Tomasz-Zdeb/Embedded-Systems-Class-Project/schematics/Embedded-Systems-Class-Project/Embedded-Systems-Class-Project.kicad_pcb

## KiCad design schematics/Rotor_kicad/Rotor_kicad.kicad_sch

Schematic: Rotor_kicad.kicad_sch

Parts:
AR2: R_Array_SIP9
C1: 1 uF
C2, C3, C4, C5, C6, C7, C8, C10, C11, C18, C19, C21, C22: 100n
C9: 150n
C12, C16, C17: 1u
C13: (no value)
C14: 470p
C15: 220u 100V
C20: 100u 100V
CN1: Mechanical section connector
CN1L: LIOD interface connector
CN1_L: .
CN2: Line interface connector
CN2B, CN2_L: Front panel
CN2L: "Debit reader"
CN3L1: LIOD cable
CN3_L: Headset
CN4: Battery
CN5_L: Coin tray
CN6: Ext safe
CN6_L: LIOD
CNA: (no value)
CNB: (no value)
CNC: (no value)
CN_COIN: Coin discriminator module
CN_LCD, CN_LCD1: LCD module cable connector
CN_LCD2: Hitachi LM039 LCD module
D1: 1FK
D2, D4: 1N4148; D_DO-35_SOD27_P7.62mm_Horizontal
D3, D16, D17, D18: ?; D_DO-41_SOD81_P10.16mm_Horizontal
D5, D6, D7, D8, D9, D10, D11, D12, D13, D14, D15: 1N4007; D_DO-41_SOD81_P10.16mm_Horizontal
D22, D24, D25: BAS16W; SOT-323_SC-70
D23: "225"; SOT-323_SC-70
DL1: F.S. LED
DL2: LED
DZ1, DZ4: .
DZ2: 2.7V
DZ3: 18V
DZ5: 8.2V
DZ6: 1N5988
F5: Fuse
H1, H2, H4, H5, H6, H7, H8: (no value)
H3: 67382
H9: 67476 hybrid
J1, J2: .
J3: (no value)
J4: Conn_02x30_Odd_Even
JP1: (no value)
L1: L_Iron
ML1: 64357/A
MR1: .
OP1, OP2, OP3, OP4: CNY17-1
PM1: 4.7K
PM2: 100K
PTC1, PTC2, PTC3, PTC4: .
Q1, Q2, Q5, Q7, Q9, Q10: BC847; SOT-23
Q3, Q4, Q6, Q8: BC857; SOT-23
Q11: Si2301; SOT-23
R1, R5: (no value)
R2, R26, R40: 10K
R3: 150
R4: 100k?
R6: 47k
R7, R25, R63, R64: 100k
R8: 120K
R9: 3.9k
R10, R11, R15, R20, R21, R22, R23: ?
R12: 8.3K 1%
R13, R14: 122 1%
R16, R29, R30, R32, R33, R39, R48, R69: 100
R17: 620K 1%
R18: 100k(?)
R19: 13K
R24, R38: 150K
R27, R28, R34, R44, R60: 100K
R31, R41: 2.2K
R35: 1K
R36: 6.8K
R37: 300K
R42: 3.3K
R43: 46K
R45, R50, R51, R58, R59: 6.5K
R46, R47: 210
R49: 10
R52, R57: 330
R53, R54, R55, R56: 220
R61: 170k
R62: 11.6k
R65, R67, R68: 10k
R66: 20.8k
RL1, RL2: SIEMENS-V23042-B2201-B101
RN1: AR1; R_Array_SIP9
SUR1: (no value)
SW: RESET
SW1: Left
SW2: Right
SW3: 3
SW4: 4
SW5: 5
SW6: 6
SW7: 7
SW8: 8
SW9: *
SW10: 0
SW11: #
SW12: SW_SPST
SWH: Hookswitch
SWR: Redial button
T1, T10: BC327; TO-92_Inline
T2, T4, T6: BC337; TO-92_Inline
T3: MPSA92; TO-92_Inline
T5, T7, T8: MPSA42; TO-92_Inline
T9: BU806
T11, T12: BC237; TO-92_Inline
U1: 74HC14
U2, U9: 74LS125
U3, U4: 74HC244
U5: HEF4093B
U6: 74HC373
U7: 74LS148
U8: 4556
U10: 4023
U11: 4001
U12: ITR9608-F; Everlight_ITR9608-F

Connections:
+5V: AR2.1 (common), C6.2, C7.2, C8.2, C9.2, C10.2, C11.2, C12.2, C13.1, CN1.2, CN1.9, CN1.43, CN1.47, CN2.12, CN2.29, CN3L1.8, CNA.3, CNA.16, CNA.17, CNA.30, CNC.23, H2.4 (VCC), H3.9 (VCC), H4.4 (VCC), H5.4 (VCC), H6.8 (VCC), H7.8 (VCC), H8.8 (VCC), H9.7, J2.4, J3.7, R1.1, R2.1, R3.1, R4.1, R5.1, R7.1, R8.1, R10.1, R11.1, R12.1, R13.1, R14.1, R25.1, R63.1, R64.1, RL1.9 (15), RL1.10 (16), RN1.1 (common), U1.20 (VCC), U2.14 (VCC), U3.20 (VCC), U4.14 (VDD), U4.20 (VCC), U5.14 (D5), U5.20 (VCC), U6.14 (VCC), U6.20 (VCC), U7.16 (VCC), U8.8 (Vss), U8.16 (Vdd), U9.14 (VCC), U10.2, U10.8, U10.14 (VDD), U11.14 (VDD)
+BATT: C14.1, CN1.36, CN1.42, CN1.44, CN1.46, CN1L.7, CN2.13, CN2.28, CN3L1.5, H1.13 (OUT), H5.15 (VBAT1), H5.16 (VBAT2), J2.15, J2.16, Q3.2 (E), R16.1, R46.1, SUR1.1 (VBAT)
AC_DIN: CN1_L.31, CN2.31, T1.1 (C)
AC_DOUT: CN1_L.9, CN2.9, H1.1 (OUT), OP2.1
AS_BRIDGE_+: C14.2, D11.1 (K), D12.1 (K), R24.2, R25.1, T5.3 (E), T6.3 (C), T7.3 (C)
AS_DIN: CN1_L.33, CN2.33, JP1.1 (A), OP3.5
AS_DOUT: CN1_L.8, CN2.8, H1.3 (OUT), OP4.1
B_A0: CNB.21, U5.3 (D0), U6.3
B_A1: CNB.12, U5.4 (D1), U6.4
B_A2: CNB.22, U5.7 (D2), U6.7 (GND)
B_A3: CNB.11, U5.8 (D3), U6.8
B_A4: CNB.23, U5.13 (D4), U6.13
B_A5: CNB.10, U5.14 (D5), U6.14 (VCC)
B_A6: CNB.24, U5.17 (D6), U6.17 (D6)
B_A7: CNB.9, U5.18 (D7), U6.18 (D7)
CLOCK: CN_LCD.3, CN_LCD2.4
CN1-21: CN1.21, CN1.38
CN1-23: CN1.23, CN1.31
CN1-53: CN1.53, H9.8
CN1L-1: CN1L.1, U1.7 (GND), U1.18 (1Y0)
CN1L-3: CN1L.3, U1.9, U1.16 (1Y1)
CN1L-4: CN1L.4, D1.1 (K), D2.1 (K)
CN1L-5: CN1L.5, CN2L.2, CN3L1.2, R22.1, R23.1, T1.2 (B)
CN2-16: H9.6
CN2-18: CN2.18, CNC.14
CN2-21: U11.3, U11.12
CN2-22: CN2.22, H4.11 (OUT), R15.2
CN2-31: R17.1, U10.1
CN2-34: CN2.34, H1.5 (OUT)
CN2L-1: CN1L.10, CN2L.1, R3.2
CN2L-3: CN2L.3, R16.2
COIN_D0: CN1.51, U7.5 (EI)
COIN_D1: CN1.48, U7.11 (I1)
COIN_D2: CN1.11, U7.12 (I2)
COIN_D3: CN1.50, U7.13 (I3)
COIN_D4: CN1.12, U7.1 (I4)
COIN_D5: CN1.49, U7.2 (I5)
COIN_D6: CN1.13, U7.3 (I6)
COIN_SW1: CN2.10, H2.3 (IN)
COIN_SW2: CN2.32, H2.2 (IN)
C_A0: CNC.28, U5.2 (O0)
C_A1: CNC.7, U5.5 (O1)
C_A2: CNC.26, U5.6 (O2)
C_A3: CNC.8, U5.9 (O3)
C_A4: CNC.25, U5.12 (O4)
C_A5: CNC.24, U5.15 (O5)
C_A6: CNC.10, U5.16 (O6)
C_A7: CNC.22, U5.19 (O7)
C_A8: CNC.11, U6.2
C_A9: CNC.9, U6.12
C_A10: CNC.27
C_D0: CNB.1, CNC.29, RN1.3 (R2), U3.18 (1Y0), U4.18 (1Y0)
C_D1: CNB.32, CNC.31, RN1.5 (R4), U3.16 (VDD), U4.16 (1Y1)
C_D2: CNB.2, CNC.2, RN1.7 (R6), U3.14 (CLK), U4.14 (VDD)
C_D3: CNB.31, CNC.3, RN1.9 (R8), U3.12 (Cout), U4.12
C_D4: CNB.3, CNC.30, RN1.8 (R7), U2.3, U3.9 (Q8), U4.9
C_D5: CNB.30, CNC.4, H2.5 (OUT), RN1.6 (R5), U2.6, U3.7 (Q3), U4.7 (VSS)
C_D6: CNB.4, CNC.5, RN1.4 (R3), U2.8, U3.5 (Q6), U4.5
C_D7: CNB.29, CNC.6, RN1.2 (R1), U2.11, U3.3 (Q0), U4.3
C_S0: CNC.19, U6.5
C_S1: CNC.21, U6.6
C_S2: CNC.15
C/~D: CN_LCD.5, CN_LCD2.8
DATA: CN_LCD.11, CN_LCD2.5
ENC0: AR2.5 (R4), C1.2, CN1.35, U3.2 (Q1)
ENC1: AR2.4 (R3), C2.2, CN1.27, U3.4 (Q2)
ENC2: AR2.6 (R5), C3.2, CN1.34, U3.6 (Q7)
ENC3: AR2.8 (R7), C4.2, CN1.28, U3.8 (VSS)
ENC4: AR2.9 (R8), C5.2, CN1.33, U3.11 (Q9)
FS_LED: CN1.6, H1.13 (OUT)
GND: C1.1, C2.1, C3.1, C4.1, C5.1, C6.1, C7.1, C8.1, C9.1, C10.1, C11.1, C12.1, C13.2, C14.2, C16.1, C17.1, C22.1, CN1.16, CN1.20, CN1.22, CN1.26, CN1.29, CN1.52, CN1.59, CN1.60, CN2.11, CN2.30, CN2L.4, CN2L.7, CN3L1.4, CN3L1.7, CN6.3, CNA.1, CNA.32, CNC.1, CNC.16, CNC.17, CNC.32, D16.2 (A), D18.2 (A), D23.1 (A), D24.1 (A), H1.14 (GND), H2.12 (GND), H3.5 (GND), H4.12 (GND), H5.1 (GND1), H5.2 (GND2), H5.6 (GND3), H5.8 (GND4), H5.9 (GND5), H5.10 (GND6), H5.17 (GND7), H5.20 (GND8), H6.5 (GND1), H6.10 (GND2), H7.5 (GND1), H7.10 (GND2), H8.5 (GND1), H8.10 (GND2), H9.1, H9.14, J2.1, J2.2, J2.6, J2.8, J2.9, J2.10, J2.11, J2.17, J2.20, J3.1, J3.14, Q1.2 (E), Q2.2 (E), Q4.3 (C), Q7.2 (E), Q9.2 (E), Q11.3 (D), R4.2, R5.1, R7.1, R9.2, R12.2, R15.2, R17.2, R18.2, R23.2, R45.2, R51.2, R53.1, R56.1, R58.2, R62.1, R65.2, R67.2, R68.1, SUR1.2 (GND1), SUR1.4 (GND2), T1.3 (E), T2.3 (C), T3.3 (E), T4.3 (E), T5.3 (E), U1.10, U2.7 (GND), U3.10 (Q4), U4.7 (VSS), U4.10, U5.7 (D2), U5.10 (GND), U6.7 (GND), U6.10, U7.4 (I7), U7.8 (GND), U7.10 (IO), U8.8 (Vss), U8.16 (Vdd), U9.7 (GND), U10.7 (VSS), U11.7 (VSS)
H4-3: H4.3 (IN), H4.5 (OUT), U3.17 (2A0)
H4-8: H4.8 (OUT2), H7.1 (IN1)
H8-4: H8.4 (IN2), U6.16 (O6)
H9-2: H9.2, U11.11
H9-11: H9.11, U4.8
H9-15: CN2.36, H9.15
HOOK: AR2.2 (R1), CN2.17, U2.2
KBD_1: CN1_L.2, CN2.2, CN2_L.15, D1.2 (A), SW4.2, SW5.2, SW6.2
KBD_2: CN1_L.1, CN2.1, CN2_L.3, D4.2 (A), SW7.2, SW8.2, SW9.2
KBD_3: CN1_L.40, CN2.40, CN2_L.14, CNB.15, R10.2, SW3.1, SW6.1, SW9.1, SW11.1
KBD_4: CN1_L.39, CN2.39, CN2_L.4, D3.2 (A), SW9.2, SW10.2, SW11.2
KBD_5: CN1_L.3, CN2.3, CN2_L.13, CNB.16, R12.2, SW1.1, SW4.1, SW7.1, SW9.1
KBD_6: CN1_L.38, CN2.38, CN2_L.5, D2.2 (A), SW1.2, SW2.2, SW3.2
KBD_7: CN1_L.4, CN2.4, CN2_L.12, CNB.18, R11.2, SW2.1, SW5.1, SW8.1, SW10.1
LCD_CLK: CN1.3, CNA.10
LCD_C/~D: CN1.5, CNA.8
LCD_MOSI: CN1.57, CNA.24
LIOD_RESET: CN3L1.10, U1.12
MCU-PC0: U5.1 (OE), U6.1
unnamed: C1.1, R3.1, U2.6, U2.11
unnamed: C1.2, D7.1 (K), D8.2 (A), R6.1, RL1.6 (9), U2.3
unnamed: C2.2, C3.2, C4.1, CN3L1.9, D2.2 (A), DZ3.1 (K), OP2.4, R9.2, R11.2, R24.1, RL2.8 (13), T2.1 (E), U1.2
unnamed: C3.1, U1.11
unnamed: C4.2, R12.1, R15.1, U1.10
unnamed: C5.1, U5.11 (LE)
unnamed: C5.2, Q11.1 (G), R62.2, U5.8 (D3), U5.9 (O3)
unnamed: C6.1, C7.1
unnamed: C6.2, R13.1
unnamed: C7.2, CN3_L.1
unnamed: C8.1, CN3_L.3, R16.2
unnamed: C8.2, C9.1, R17.2, U1.1
unnamed: C10.1, U1.5, U1.8
unnamed: C2.1, C10.2, C11.1, C12.2, C13.1, CN3_L.4, D5.2 (A), D7.2 (A), DZ3.2 (A), R10.1, R12.2, R18.1, R19.2, RL2.7 (11), U1.3, U1.9
unnamed: C9.2, C12.1, R17.1, U1.16 (1Y1)
unnamed: C13.2, R12.1, R15.2
unnamed: C14.1, OP4.5, R24.1, T7.2 (B)
unnamed: C15.1, D4.1 (K)
unnamed: C15.2, D9.2 (A), D10.2 (A), DL2.1 (K), DZ6.2 (A), R29.2, R42.1
unnamed: C18.1, R35.1, R36.2, T10.2 (B)
unnamed: C18.2, R34.2, R36.1, T10.3 (E), U2.8
unnamed: C19.1, U6.11, U6.12
unnamed: C19.2, Q11.2 (S), R65.1, U6.9
unnamed: C20.1, D13.2 (A), DZ5.1 (K), F5.2
unnamed: C20.2, CN4.1, DZ5.2 (A)
unnamed: C21.1, D24.3 (K), R67.1, U6.1
unnamed: C21.2, U6.3, U6.6
unnamed: C22.2, D25.3 (K), R68.2, U6.5
unnamed: CN1.40, R16.2
unnamed: CN1L.6, SUR1.3 (UNK)
unnamed: CN1L.9, CN1L.11, CN1L.12
unnamed: CN1_L.5, CN2_L.11
unnamed: CN1_L.10, CN5_L.4
unnamed: CN1_L.12, CN1_L.15
unnamed: CN1_L.14, CN6_L.2
unnamed: CN1_L.17, T11.1 (C)
unnamed: CN1_L.18, CN6_L.4
unnamed: CN1_L.22, CN6.5
unnamed: CN1_L.24, R39.1
unnamed: CN1_L.25, CN6_L.3
unnamed: CN1_L.27, CN6_L.1
unnamed: CN1_L.32, CN5_L.2
unnamed: CN1_L.34, CN6_L.10
unnamed: CN1_L.36, CN2_L.9
unnamed: CN2B.1, SWH.1 (A)
unnamed: CN2B.2, SWH.3 (C)
unnamed: CN2B.7, SWR.2 (B)
unnamed: CN2B.8, SWH.6 (C)
unnamed: CN2B.10, SWH.5 (B)
unnamed: CN2B.11, SWR.3 (C)
unnamed: CN2B.16, SWH.2 (B)
unnamed: CN2L.5, SUR1.5 (UNK2)
unnamed: CN2L.8, R10.1
unnamed: CN2L.9, D1.2 (A), R21.2
unnamed: CN2L.10, R10.2, T3.1 (C)
unnamed: CN2_L.1, MR1.2
unnamed: CN2_L.2, MR1.1
unnamed: CN2_L.6, CN2_L.8
unnamed: CN2_L.7, R39.2
unnamed: CN2_L.10, R40.1
unnamed: CN2_L.16, MR1.3
unnamed: CN3L1.1, R17.1, U1.6
unnamed: CN3L1.3, R18.1, U1.4
unnamed: CN3_L.2, R14.1
unnamed: CN4.2, F5.1
unnamed: CN5_L.1, CN5_L.3
unnamed: CN6.1, R33.2
unnamed: CN6.2, CN6.4, R32.1
unnamed: CN6_L.5, R25.2
unnamed: CN6_L.9, CN6_L.11, CN6_L.12
unnamed: CN_LCD1.1, J4.1
unnamed: CN_LCD1.2, J4.3
unnamed: CN_LCD1.3, J4.5
unnamed: CN_LCD1.4, J4.7
unnamed: CN_LCD1.5, J4.9
unnamed: CN_LCD1.6, J4.11
unnamed: CN_LCD1.7, J4.13
unnamed: CN_LCD1.8, J4.14
unnamed: CN_LCD1.9, J4.12
unnamed: CN_LCD1.10, J4.10
unnamed: CN_LCD1.11, J4.8
unnamed: CN_LCD1.12, J4.6
unnamed: CN_LCD1.13, J4.4
unnamed: CN_LCD1.14, J4.2
unnamed: CN_LCD.1, SW.1
unnamed: CN_LCD.2, CN_LCD2.2
unnamed: CN_LCD.6, CN_LCD2.10, DL1.2 (A)
unnamed: CN_LCD.7, SW2.2
unnamed: CN_LCD.8, SW1.1
unnamed: CN_LCD.13, CN_LCD.14, CN_LCD2.1, PM1.1, PM1.2, SW1.2
unnamed: D1.1 (K), OP2.5, R8.1, U8.11 (~Q1)
unnamed: D2.1 (K), U8.12 (~Q0)
unnamed: D2.2 (A), DZ4.1 (K), DZ5.2 (A), PTC3.2
unnamed: D3.1 (K), U8.9 (~Q3)
unnamed: D4.1 (K), U8.10 (~Q2)
unnamed: D4.2 (A), OP4.4, R26.1, R27.1, R28.1, R31.2, T5.1 (C), T8.3 (C)
unnamed: D5.1 (K), D6.2 (A), DZ1.1 (K), PTC1.2
unnamed: D6.1 (K), D8.1 (K), DZ2.1 (K), R4.1
unnamed: D2.1 (K), D10.1 (K), D12.2 (A), DZ5.1 (K), R23.1
unnamed: D9.1 (K), D11.2 (A), DZ4.2 (A), OP3.2, PTC4.2
unnamed: D13.1 (K), D14.2 (A)
unnamed: D14.1 (K), D15.2 (A)
unnamed: D3.2 (A), D16.1 (K), J2.12, Q6.3 (C), Q7.3 (C)
unnamed: D3.1 (K), D17.1 (K), Q3.3 (C), Q4.2 (E), Q6.2 (E), Q8.2 (E), R48.1, R54.2, R55.2
unnamed: D17.2 (A), D18.1 (K), J2.18, Q8.3 (C), Q9.3 (C)
unnamed: D22.1 (A), R66.1
unnamed: D22.3 (K), U5.1 (OE), U5.2 (O0), U5.4 (D1)
unnamed: D23.3 (K), R61.2, R66.2, U5.5 (O1)
unnamed: D25.1 (A), R69.2
unnamed: DL1.1 (K), DL2.2 (A), R3.1
unnamed: DL1.2 (A), R28.2, T8.2 (B)
unnamed: DZ1.2 (A), PTC2.2, R3.2, RL1.8 (13)
unnamed: DZ2.2 (A), OP1.2, R7.1, R8.2, RL2.6 (9), T2.3 (C), T3.1 (C)
unnamed: DZ6.1 (K), R29.1
unnamed: H1.15 (IN), H9.3
unnamed: H2.6 (OUT), U4.17 (2A0)
unnamed: H2.7 (OUT1), U4.13
unnamed: H3.2 (OUT), U2.5
unnamed: H3.4 (OUT), U2.12
unnamed: H3.6 (OUT), U4.15 (2A1)
unnamed: H3.7 (OUT), U2.9
unnamed: H3.10 (IN), R7.2, R9.2
unnamed: H4.6 (OUT), H6.1 (IN1)
unnamed: H4.7 (OUT1), U3.13 (CKEN)
unnamed: H4.9 (IN), U4.1, U4.19 (2OE), U8.7 (~Q3)
unnamed: H4.10 (IN), U2.1, U2.4, U2.10, U2.13, U8.5 (~Q1)
unnamed: H5.7 (DRV_EN), U11.4
unnamed: H6.4 (IN2), U6.15 (O5)
unnamed: H7.4 (IN2), U6.9
unnamed: H9.4, JP1.2 (B), R5.2
unnamed: H9.5, U10.5
unnamed: H9.10, U10.4
unnamed: H9.12, U10.3
unnamed: J1.1, R60.2, U1.1, U1.12
unnamed: J1.2, U1.2
unnamed: J1.3, U1.3, U1.8, U1.9
unnamed: J1.4, U1.6
unnamed: J1.6, U1.10
unnamed: J1.7, U1.13
unnamed: J1.5, J1.10
unnamed: J2.3, Q2.1 (B), U4.12
unnamed: J2.5, U4.8
unnamed: J2.7, U4.1, U4.2
unnamed: J3.2, U5.6 (O2)
unnamed: J3.3, R61.1, U5.3 (D0)
unnamed: J3.4, R63.2, U5.12 (O4)
unnamed: J3.5, U5.10 (GND)
unnamed: J3.6, R64.2, U5.13 (D4)
unnamed: J3.8, U6.13
unnamed: J3.9, U6.10
unnamed: J3.10, U6.8
unnamed: J3.11, U6.4
unnamed: J3.12, U6.2
unnamed: J3.13, R69.1
unnamed: ML1.4 (I_LIMIT), R43.1
unnamed: ML1. (GND), ML1.2 (GND), R44.2, T12.3 (E)
unnamed: MR1.4, RL1.7 (11)
unnamed: MR1.6, PTC1.1
unnamed: MR1.7, PTC2.1
unnamed: MR1.8, PTC3.1
unnamed: MR1.9, PTC4.1
unnamed: OP1.1, R4.2
unnamed: OP1.5, R5.2
unnamed: OP3.1, R23.2
unnamed: PM1.1, PM1.2, R30.1
unnamed: PM1.3, R42.2, T9.1 (B)
unnamed: PM2.1, R38.1
unnamed: PM2.2, U2.5
unnamed: PM2.3, R37.2
unnamed: Q1.1 (B), R22.2, R45.1
unnamed: Q1.3 (C), R47.2
unnamed: Q2.3 (C), R49.2
unnamed: Q3.1 (B), R46.2, R47.1
unnamed: Q4.1 (B), R48.2, R49.1
unnamed: Q5.1 (B), R50.2, R51.1
unnamed: Q5.2 (E), Q7.1 (B), R53.2
unnamed: Q5.3 (C), R52.2
unnamed: Q6.1 (B), R54.1, R57.1
unnamed: Q8.1 (B), R52.1, R55.1
unnamed: Q10.1 (B), R58.1, R59.1
unnamed: Q9.1 (B), Q10.2 (E), R56.2
unnamed: Q10.3 (C), R57.2
unnamed: R1.1, R2.1
unnamed: R1.2, T2.1 (E), U2.1, U3.14 (CLK)
unnamed: R2.1, R20.2, T6.2 (B)
unnamed: R2.2, U3.5 (Q6)
unnamed: R3.1, R4.1, T2.2 (B)
unnamed: R3.2, SW2.1
unnamed: R5.1, R6.2, T1.2 (B)
unnamed: R5.2, U1.2, U1.14 (VCC)
unnamed: R6.1, T1.3 (E)
unnamed: R6.2, U2.2
unnamed: R7.2, T3.2 (B), U1.5, U1.11
unnamed: R8.2, R9.1, T3.2 (B)
unnamed: R9.1, T2.2 (B), T3.3 (E)
unnamed: R10.2, U1.14 (VCC)
unnamed: R11.1, R12.2, U1.6
unnamed: R11.2, T4.1 (C), U1.13
unnamed: R12.1, T4.2 (B)
unnamed: R13.2, U1.12
unnamed: R14.2, U1.13
unnamed: R15.1, R16.1, T5.2 (B)
unnamed: R18.2, U1.7 (GND)
unnamed: R19.1, U1.4
unnamed: R20.1, T6.3 (C)
unnamed: R21.1, T6.1 (E)
unnamed: R22.1, U4.11
unnamed: R22.2, U3.9 (Q8)
unnamed: R24.2, T1.1 (C)
unnamed: R26.2, T5.2 (B), T6.1 (E)
unnamed: R27.2, T6.2 (B), T7.1 (E)
unnamed: R30.2, T8.1 (E)
unnamed: R31.1, T9.2 (C)
unnamed: R34.1, U2.3
unnamed: R35.2, U2.7 (GND)
unnamed: R37.1, T10.1 (C)
unnamed: R40.2, R41.1, T11.2 (B)
unnamed: R41.2, T11.3 (E)
unnamed: R43.2, R44.1, T12.2 (B)
unnamed: R50.1, U4.4
unnamed: R59.2, U4.6, U4.10
unnamed: RL2.9 (15), RL2.10 (16)
unnamed: T5.1 (C), U1.15 (2A1)
unnamed: U1.1, U2.9, U2.10
unnamed: U1.8, U2.12, U3.15 (Reset)
unnamed: U1.5, U1.11
unnamed: U1.5, U1.12
unnamed: U1.19 (2OE), U2.8
unnamed: U2.4, U2.5
unnamed: U3.1 (Q5), U3.19 (2OE), U8.6 (~Q2)
unnamed: U4.2, U7.9 (S0)
unnamed: U4.4, U7.7 (S1)
unnamed: U4.6, U7.6 (S2)
unnamed: U4.3, U4.5, U4.9, U4.13
unnamed: U10.6, U10.12
unnamed: U11.5, U11.10
PA0: CNA.26, H1.2 (IN)
PA1: CNA.7, H1.8 (IN)
PA2: CNA.27, H1.11 (IN)
PA3: CNA.6, U10.9
PA4: CNA.28, H1.4 (IN)
PA5: CNA.5
PA6: CNA.29, U8.14 (A0)
PA7: CNA.4, U8.13 (A1)
PB0: CNA.22, U11.1, U11.2
PB1: CNA.11, H1.6 (IN)
PB2: CNA.23, H2.9 (IN)
PC0: CN2.23, CNA.18, U8.1 (~EN), U8.15 (~EN), U10.11, U10.13, U11.6, U11.13
PC1: CN1.10, CNA.15
PC2: CNA.19, CNC.18, R2.2
PC3: CNA.14, H8.1 (IN1)
PC4: CNA.20, H2.10 (IN)
PC5: CN2.25, CNA.13, R3.2
PC6: CN2.27, CNA.21, R4.2
PD4: CNB.19, H9.9
PD5: CNB.14
PHOTO_POCKET: CN1.39, H3.8 (IN)
PHOTO_R_EXIT: CN1.45, R8.2, R9.1
PHOTO_R_IN: CN1.32, H3.1 (IN)
PHOTO_R_IN_PWR: CN1.30, CN2.24, H4.13 (OUT)
PHOTO_R_POCKET_PWR: CN1.17, R15.1
PHOTO_SAFE: CN1.41, H3.3 (IN)
REDIAL: CN2.5, H2.1 (IN)
RL1-R: CN1_L.6, CN2.6, H2.13 (OUT), RL1.1
RL1-S: CN1_L.37, CN2.37, H2.11 (OUT), RL1.2
RL2-R: CN1_L.7, CN2.7, H1.7 (OUT), RL2.1
RL2-S: CN1_L.35, CN2.35, H1.10 (OUT), RL2.2
R_MOT_A: CN1.24, H5.18 (MOT2)
R_MOT_B: CN1.37, H5.12 (MOT1)
SAFE_SW1: AR2.3 (R2), C17.2, CN1_L.19, CN2.19, R33.1, U4.11
SAFE_SW2: AR2.7 (R6), C16.2, CN1_L.20, CN2.20, R32.2, U3.15 (Reset)
SCL-39: CN2.15, CNB.17
SCL-43: CNB.25, U11.8, U11.9
SCL-44: CNB.8, H5.5 (DIR)
SCL-45: CNB.26, H5.3 (~RUN/STOP)
SCL-46: CN2.14, CNB.7
SCL-47: CNB.27, U5.11 (LE)
SCL-50: CNB.6, U6.11
SCL-51: CNB.28, U8.2 (A0)
SCL-52: CNB.5, U8.3 (A1), U8.4 (~Q0)
SOLENOID_C_PATH: CN1.19, H6.9 (SOL)
SOLENOID_C_REJ: CN1.15, H7.9 (SOL)
SOLENOID_R_POCKET: CN1.25, H8.9 (SOL)
SW1: CN1.54, CNB.13, R14.2
SW2: CN1.7, CNB.20, R13.2
SW_C_PATH: CN1.18, H4.1 (IN)
SW_C_REJ: CN1.14, H4.2 (IN)
V0: CN_LCD.12, CN_LCD2.3
~BUSY: CN_LCD.10, CN_LCD2.7, R2.2
~CS: CN_LCD.4, CN_LCD2.6
~IRQ: CNA.31, U10.10
~I_LIMIT: CN1_L.26, CN2.26, CNA.12, R1.2, T12.1 (C)
~LCD_BUSY: CN1.56, CNA.25
~LCD_CS: CN1.4, CNA.9
~LCD_RESET: CN1.55, U6.19 (O7)
~LIOD_RESET_BUFF: R8.1, R25.2, U1.3
~LIOD_RESET: CN1L.2, U1.17 (2A0), U2.13
~RST: CN1.1, CNA.2, CN_LCD.9, CN_LCD2.9, R1.2

Notes on the sheet:
No designators present on module. Resistors are thick-film on ceramic, laser trimmed. Reported values are direct measures.
Might be a zener
No designators present on module. Resistor are thick-film on ceramic, laser trimmed. Reported values are direct measures.
Pin numbering on silkscreen doesn't match schematic
Coin reject solenoid
Power regulation
Hookswitch
Rotor motor
Coin reject sw
Mode switches: Both ON/Both OFF -> Normal mode SW1 ON, SW2 OFF -> Config mode SW1 OFF, SW2 ON -> Test mode
Power monitoring
On some boards, single IC (PT2)
6V lead acid (charged to 6.75)
Connectors
Rotor input photointerrupter
Data comm. line (Power is derived from here)
Power
Main terminal strip
LCD
Voice circuit
Coin-in-safe photointerrupter
Coin path switch
Rotor absolute encoder
Rotor pocket solenoid
Rotor exit photointerrupter
On some boards, replaced by IC (PT1)
Rotor pocket photointerrupter
Coin disc.
Coin path solenoid
Stacked w/the cable connector
